WiHarper/nfc_card/gallery/antenna.png

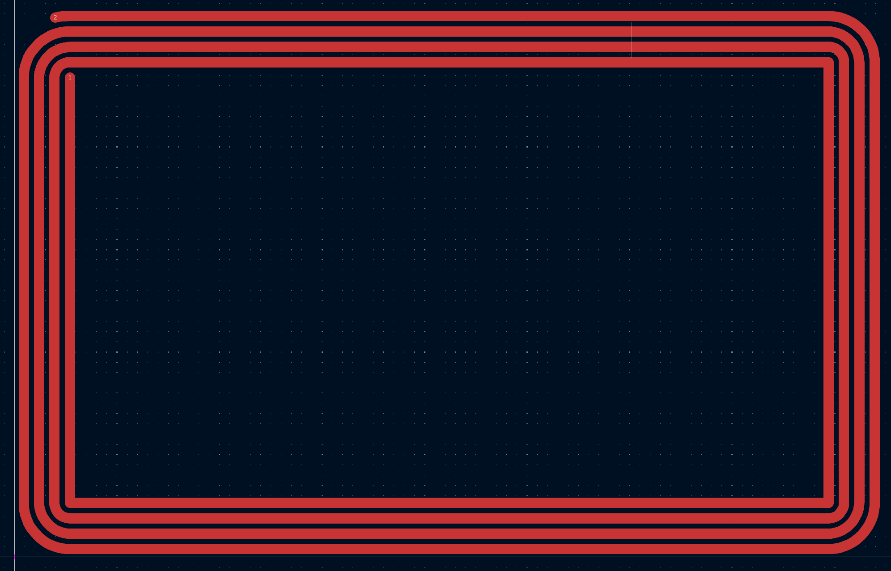
gallery/antenna.png
