WiHarper/nfc_card/gallery/back.png

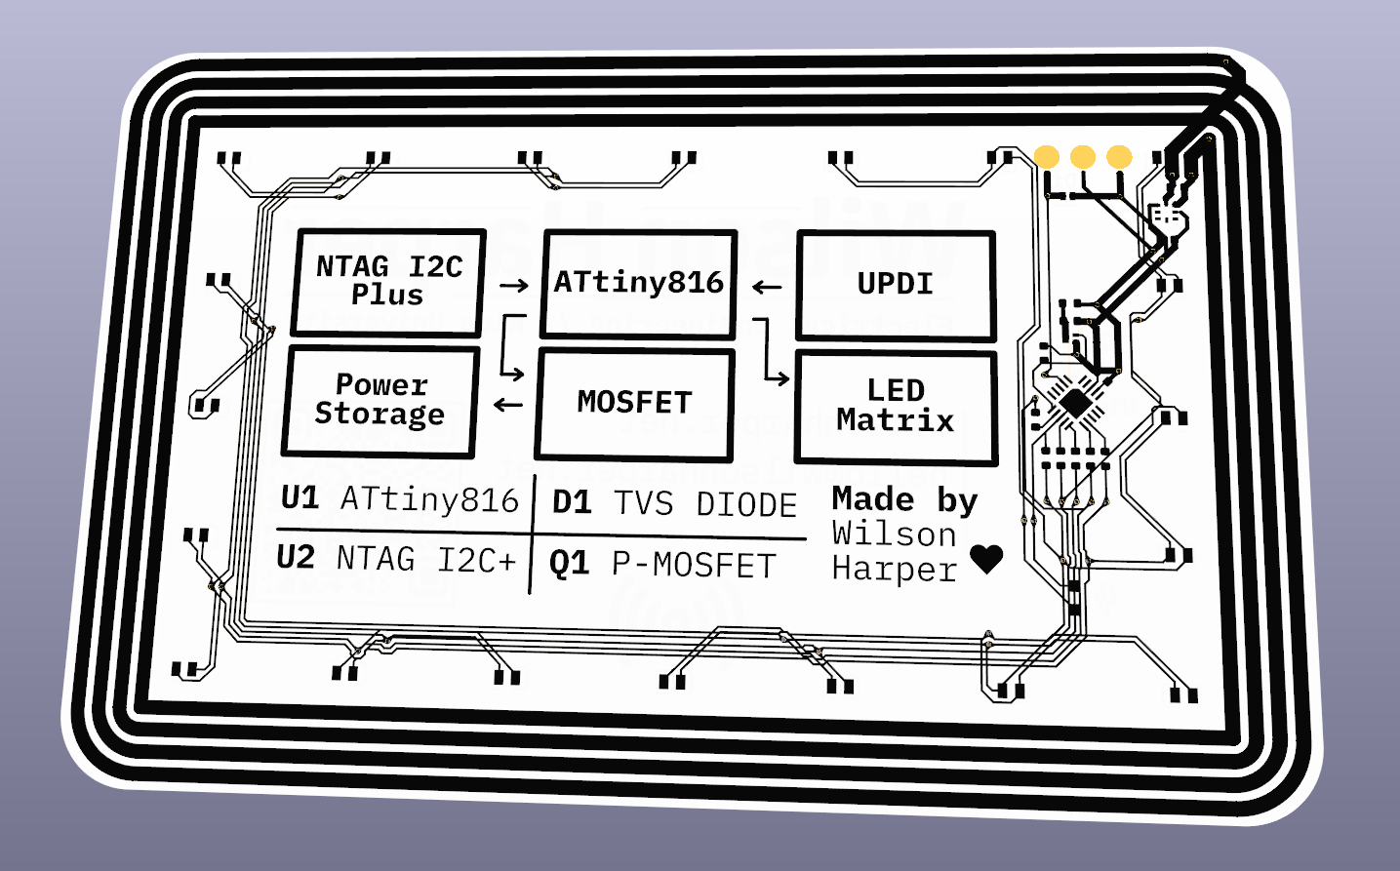
gallery/back.png
