WiHarper/nfc_card/gallery/c_traces.png

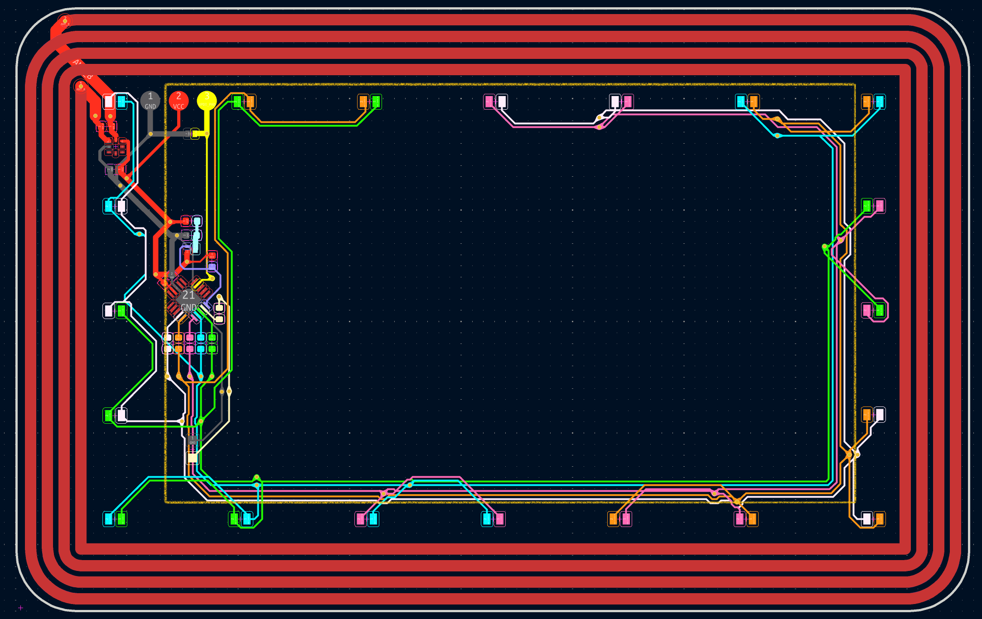
gallery/c_traces.png
