WiHarper/nfc_card/gallery/connected_to_led.jpg

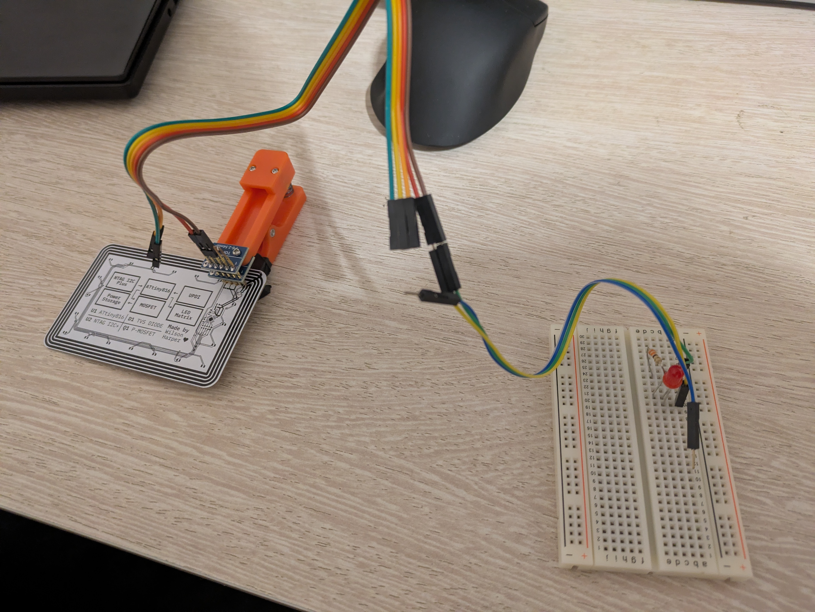
gallery/connected_to_led.jpg
