WiHarper/nfc_card/gallery/on_phone.jpg

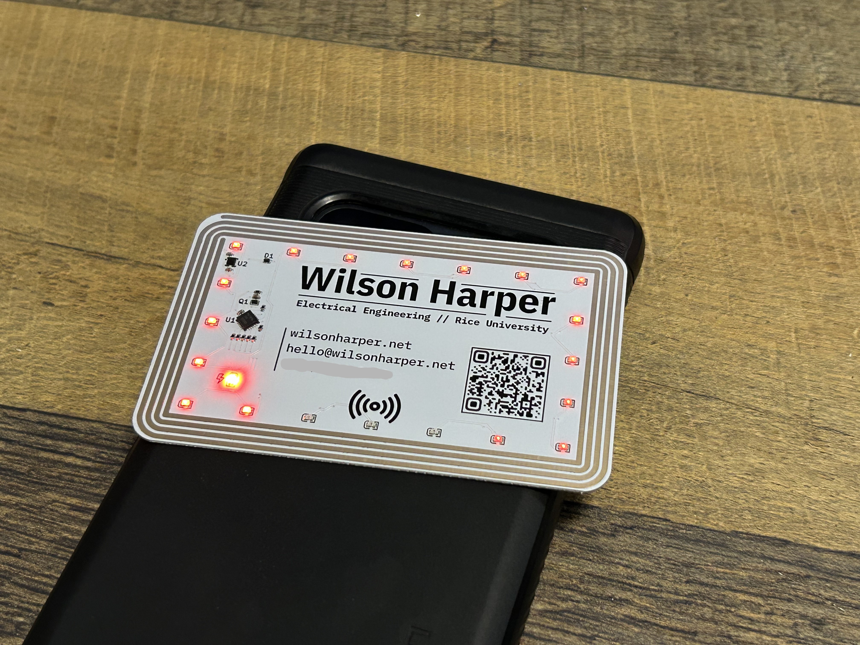
gallery/on_phone.jpg
