WiHarper/nfc_card/gallery/on_phone_2.jpg

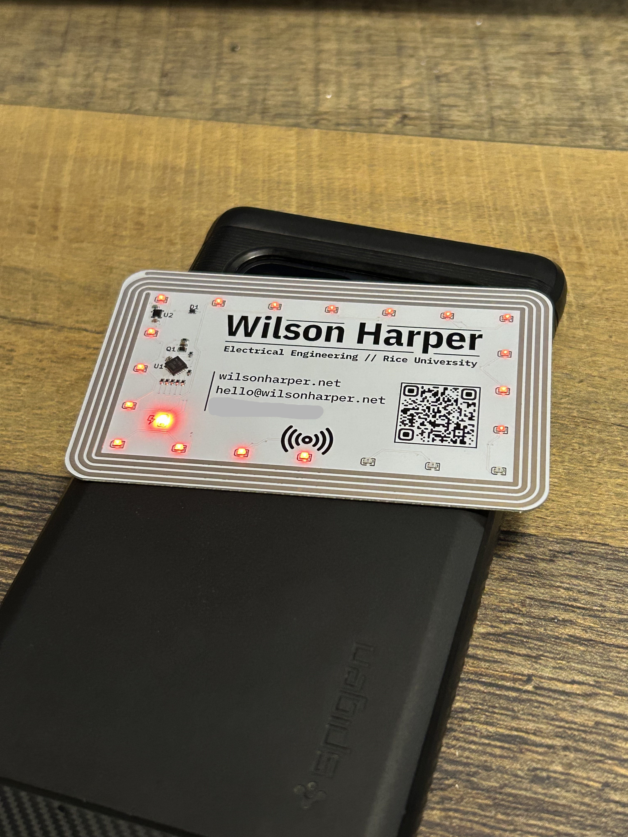
gallery/on_phone_2.jpg
