WiHarper/nfc_card/gallery/pads.png

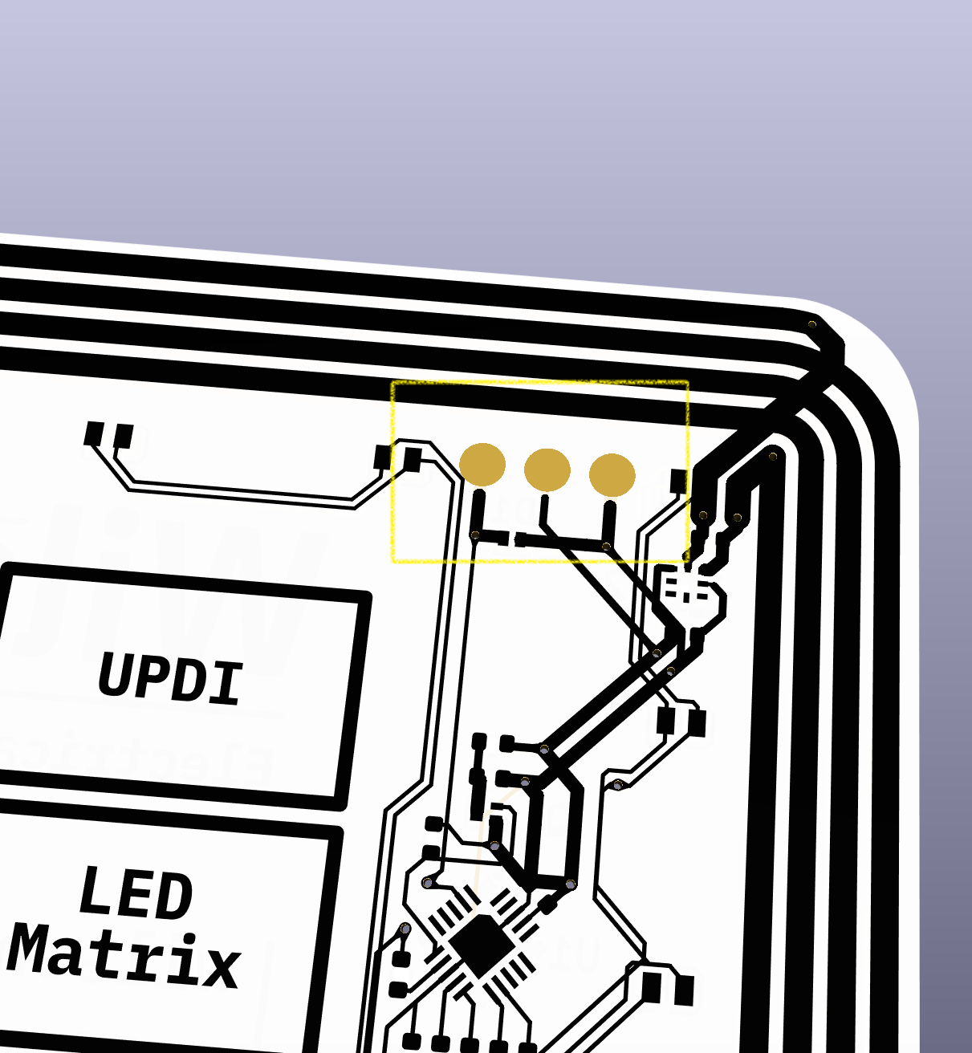
gallery/pads.png
