WiHarper/nfc_card/gallery/programming.jpg

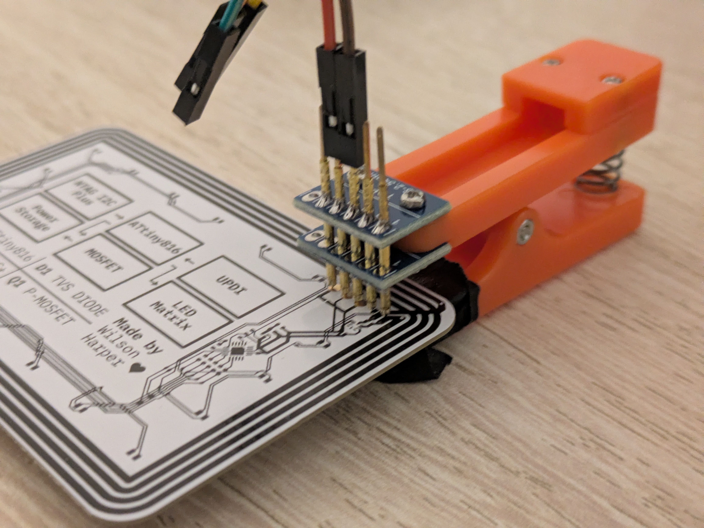
gallery/programming.jpg
