WiHarper/nfc_card/gallery/programming_2.jpg

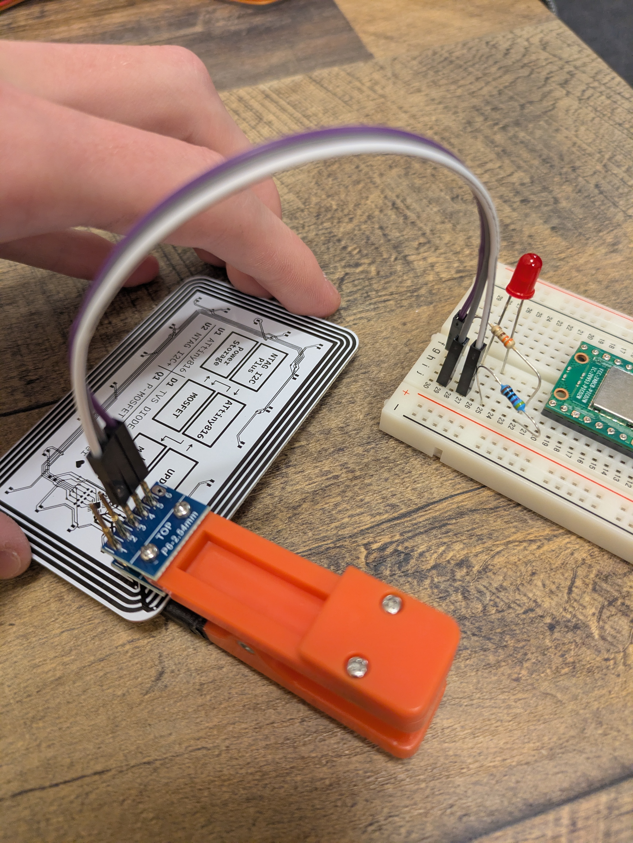
gallery/programming_2.jpg
