WiHarper/nfc_card/gallery/stack.jpg

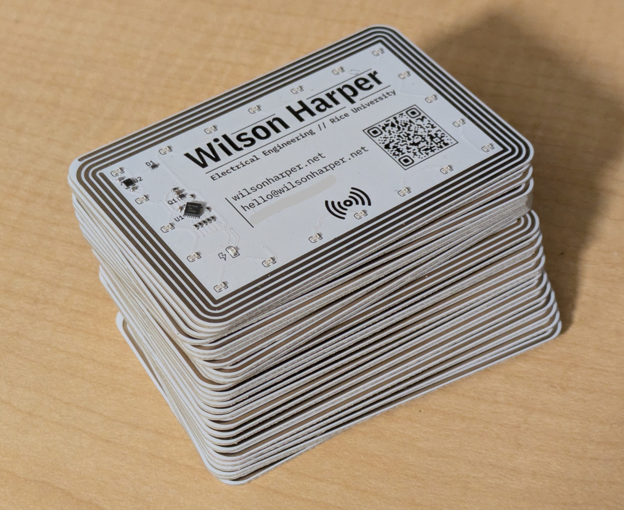
gallery/stack.jpg
