WiHarper/nfc_card/gallery/thumb.jpg

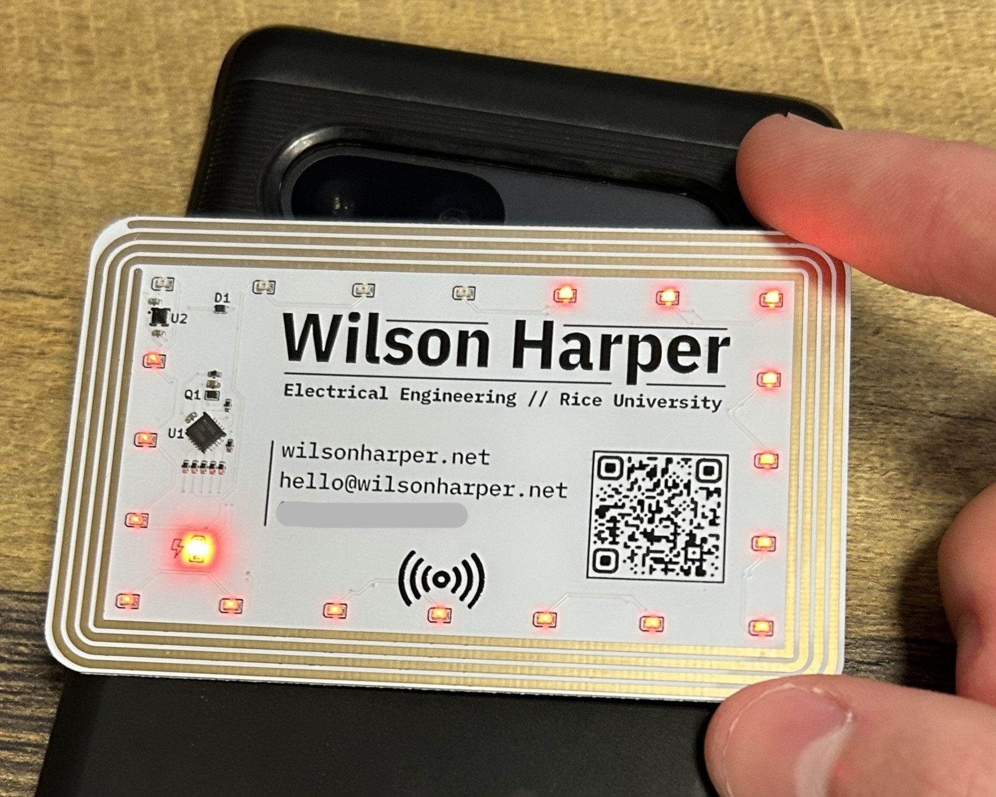
gallery/thumb.jpg
